papsdroidfr/SinS/_docs/20200711_155131.jpg

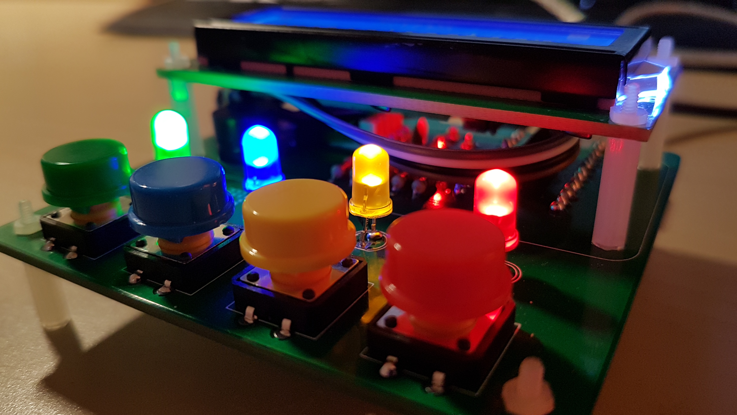
_docs/20200711_155131.jpg
